McOrts/Anemometro_IoT_MQTT_KNX/Anemometro_IoT_LoRaWAN/settings_mio.h

// LoRaWAN Configuration

/* OTAA para*/
static uint8_t devEui[] = { 0x70, 0xB3, 0xD5, 0x7E, 0xD0, 0x05, 0xDF, 0x0E };
static uint8_t appEui[] = { 0xBE, 0xFB, 0xCA, 0xAC, 0x24, 0x26, 0xA3, 0xB8 };
static uint8_t appKey[] = { 0x28, 0x98, 0x5D, 0x35, 0xEB, 0xA4, 0x5A, 0x47, 0x7F, 0xE9, 0xE2, 0xA2, 0x06, 0x4F, 0xC0, 0x40 };

uint16_t userChannelsMask[6]={ 0x00FF,0x0000,0x0000,0x0000,0x0000,0x0000 };
static DeviceClass_t lorawanClass = LORAWAN_CLASS;

// Devise location
const float latitude = 39.573;
const float longitude = 2.732;
const int alt = 20;

// Other params
float SensorId= 10.01;// Sensor  identifcator number 
const int DutyCycle = 300000; // Transmision and reading period
